3lyktrik/cleanwaterrobotics/worksheets/7 - AI Αισθητήρας χειρονομιών και προσώπων.odt

# Φύλλο Εργασίας 7 AI Αισθητήρας χειρονομιών και προσώπων

## Δραστηριότητα 1

Μπείτε στο https://wiki.dfrobot.com/sen0626/ και κάντε το παράδειγμα “1. Example Code for Arduino-Reading Data via I2C”.

Επισημαίνεται ότι για να λειτουργήσει ο αισθητήρας πρέπει να εγκαταστήσετε στο Arduino IDE δύο απαραίτητες βιβλιοθήκες, που μπορείτε να κατεβάσετε από εδώ:

https://github.com/DFRobot/DFRobot_GestureFaceDetection

https://github.com/DFRobot/DFRobot_RTU

Για οδηγίες εγκατάστασης βιβλιοθηκών δείτε εδώ: https://docs.arduino.cc/software/ide-v1/tutorials/installing-libraries/#.UxU8mdzF9H0

Μετά την εγκατάσταση των βιβλιοθηκών, ο κώδικας του παραδείγματος θα βρίσκεται και στη διαδρομή: Αρχείο -> Παραδείγματα -> DFRobot_GestureFaceDetection -> I2C -> detectGesture

## Δραστηριότητα 2

Επαληθεύστε ότι ο αισθητήρας αναγνωρίζει τη χειρονομία, σύμφωνα με τον παρακάτω πίνακα:

Χρώμα LED | Χειρονομία
Μπλε | Πολύ καλά
Πράσινο | ΟΚ
Κόκκινο | Στοπ
Κίτρινο | Το σήμα της νίκης
Μωβ | Τηλεφώνησέ μου
