3lyktrik/cleanwaterrobotics/worksheets/9 - Δέκτης GPS.odt

# Φύλλο Εργασίας 9 Δέκτης GPS

## Δραστηριότητα

Μπείτε στο https://wiki.dfrobot.com/tel0157/ και κάντε το παράδειγμα “1. Usage Example for Arduino-Read Data via I2C (https://wiki.dfrobot.com/tel0157/docs/22216) ”.

Πρέπει να εγκαταστήσετε στο Arduino IDE την παρακάτω βιβλιοθήκη:

DFRobot GNSS Library (https://github.com/DFRobot/DFRobot_GNSS)

Για οδηγίες εγκατάστασης βιβλιοθηκών δείτε εδώ: https://docs.arduino.cc/software/ide-v1/tutorials/installing-libraries/#.UxU8mdzF9H0
