3lyktrik/cleanwaterrobotics/programs/AppInventor/CatamaranControlApp1.png

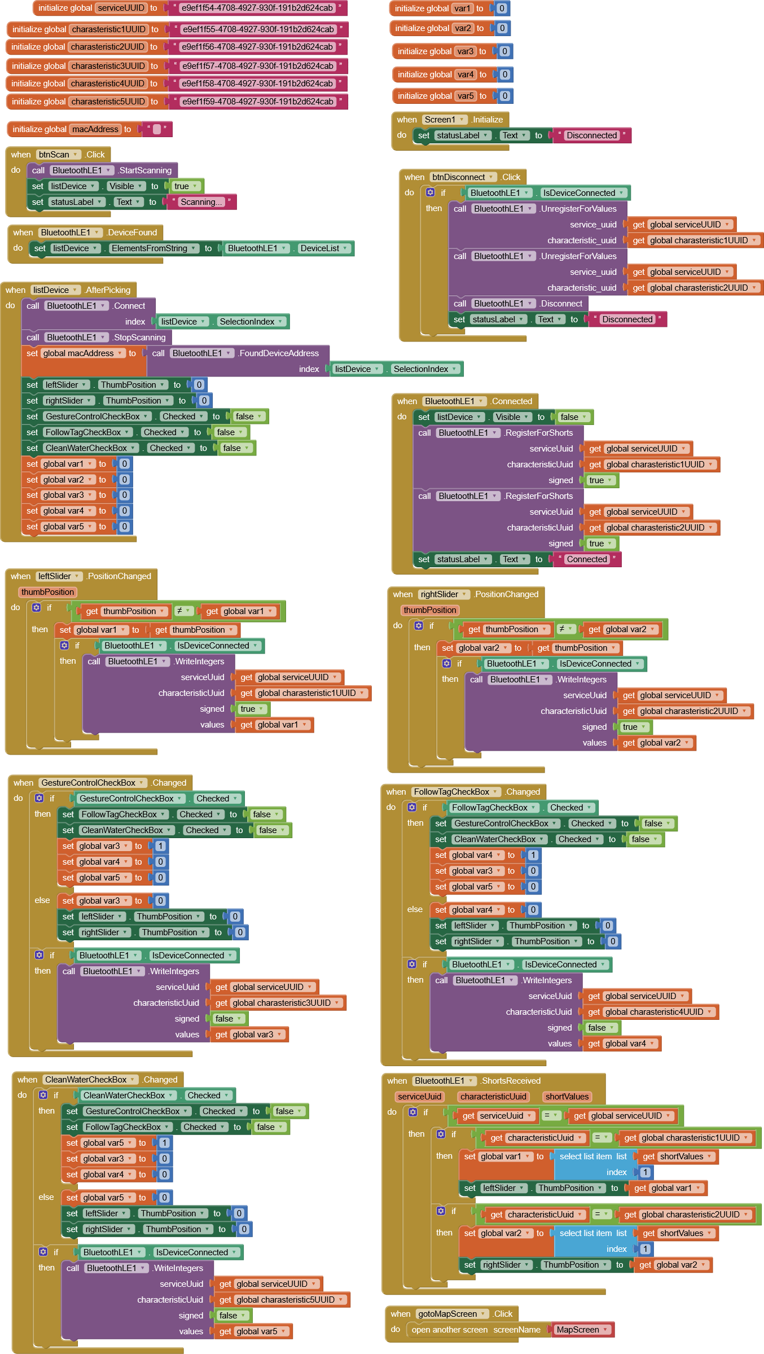
programs/AppInventor/CatamaranControlApp1.png
