3lyktrik/cleanwaterrobotics/programs/AppInventor/CatamaranControlApp2.png

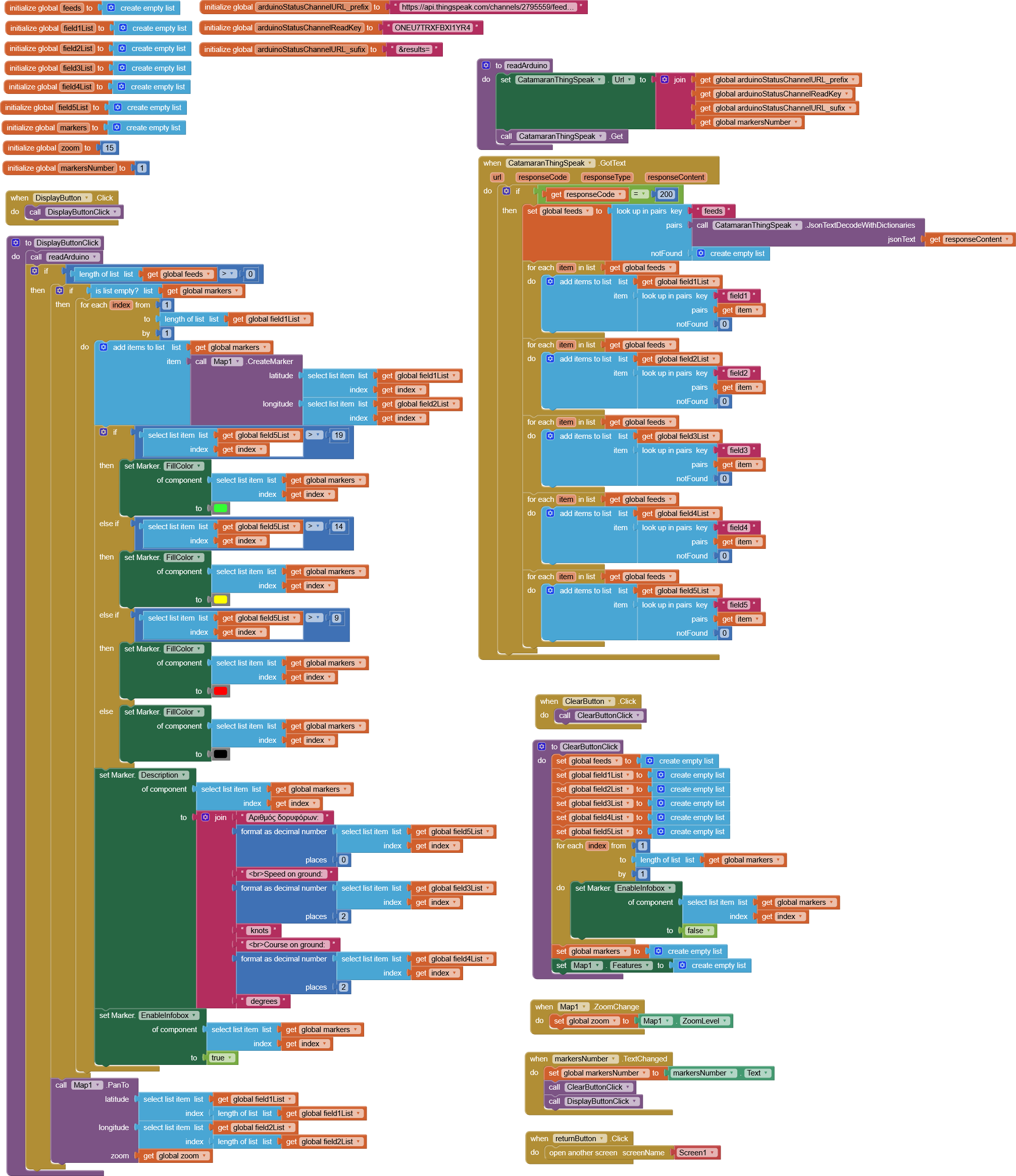
programs/AppInventor/CatamaranControlApp2.png
