3lyktrik/cleanwaterrobotics/programs/arduino/secrets.h

// Use this file to store all of the private credentials 
// and connection details

// βάλτε τους κωδικούς του WiFi
#define SECRET_SSID "ΧΧΧΧΧΧΧΧΧΧΧ"		// WiFi network name
#define SECRET_PASS "*********"	    // WiFi password

#define SECRET_CH_ID 1234567    			            // my channel number
#define SECRET_WRITE_APIKEY "ΧΧΧΧΧΧΧΧΧΧΧΧΧΧΧΧ"    // my channel write API Key
#define SECRET_READ_APIKEY "ΧΧΧΧΧΧΧΧΧΧΧΧΧΧΧΧ"     // my channel read API Key
